polesskiy-dev/iot-risk-logger-stm32l4/firmware/iot-risk-logger-stm32l4/Core/Inc/main.h

#define NFC_INT_N_Pin GPIO_PIN_0
#define NFC_INT_N_GPIO_Port GPIOA
#define NFC_INT_N_EXTI_IRQn EXTI0_IRQn
#define LIGHT_INT_N_Pin GPIO_PIN_1
#define LIGHT_INT_N_GPIO_Port GPIOA
#define LIGHT_INT_N_EXTI_IRQn EXTI1_IRQn
#define USB_VBUS_SENSE_Pin GPIO_PIN_8
#define USB_VBUS_SENSE_GPIO_Port GPIOA
#define USB_VBUS_SENSE_EXTI_IRQn EXTI9_5_IRQn
#define I2C1_SCL_SENS_Pin GPIO_PIN_9
#define I2C1_SCL_SENS_GPIO_Port GPIOA
#define I2C1_SDA_SENS_Pin GPIO_PIN_10
#define I2C1_SDA_SENS_GPIO_Port GPIOA
#define LED_N_Pin GPIO_PIN_15
#define LED_N_GPIO_Port GPIOA
#define TEMP_RESET_N_Pin GPIO_PIN_4
#define TEMP_RESET_N_GPIO_Port GPIOB
#define TEMP_INT_Pin GPIO_PIN_5
#define TEMP_INT_GPIO_Port GPIOB
#define TEMP_INT_EXTI_IRQn EXTI9_5_IRQn
#define IMU_INT1_Pin GPIO_PIN_6
#define IMU_INT1_GPIO_Port GPIOB
#define IMU_INT1_EXTI_IRQn EXTI9_5_IRQn
#define IMU_INT2_Pin GPIO_PIN_7
#define IMU_INT2_GPIO_Port GPIOB
#define IMU_INT2_EXTI_IRQn EXTI9_5_IRQn
