polesskiy-dev/iot-risk-logger-stm32l4/firmware/iot-risk-logger-stm32l4/app/core/gpio_ext_interrupts/gpio_ext_interrupts.h

/*!
 * @file gpio_ext_interrupts.h
 * @brief Brief description of the file.
 *
 * Detailed description of the file.
 *
 * @date 07/10/2024
 * @author artempolisskyi
 */

#ifndef GPIO_EXT_INTERRUPTS_H
#define GPIO_EXT_INTERRUPTS_H

#ifdef __cplusplus
extern "C" {
#endif

#include <stdio.h>

#include "main.h"


#ifdef __cplusplus
}
#endif

#endif //GPIO_EXT_INTERRUPTS_H
